ponchick/ZS-Scorpion-256-Turbo-Plus/Scorpion/Scorpion.kicad_sch

## KiCad design Scorpion/Scorpion.kicad_sch (2023-03-14)

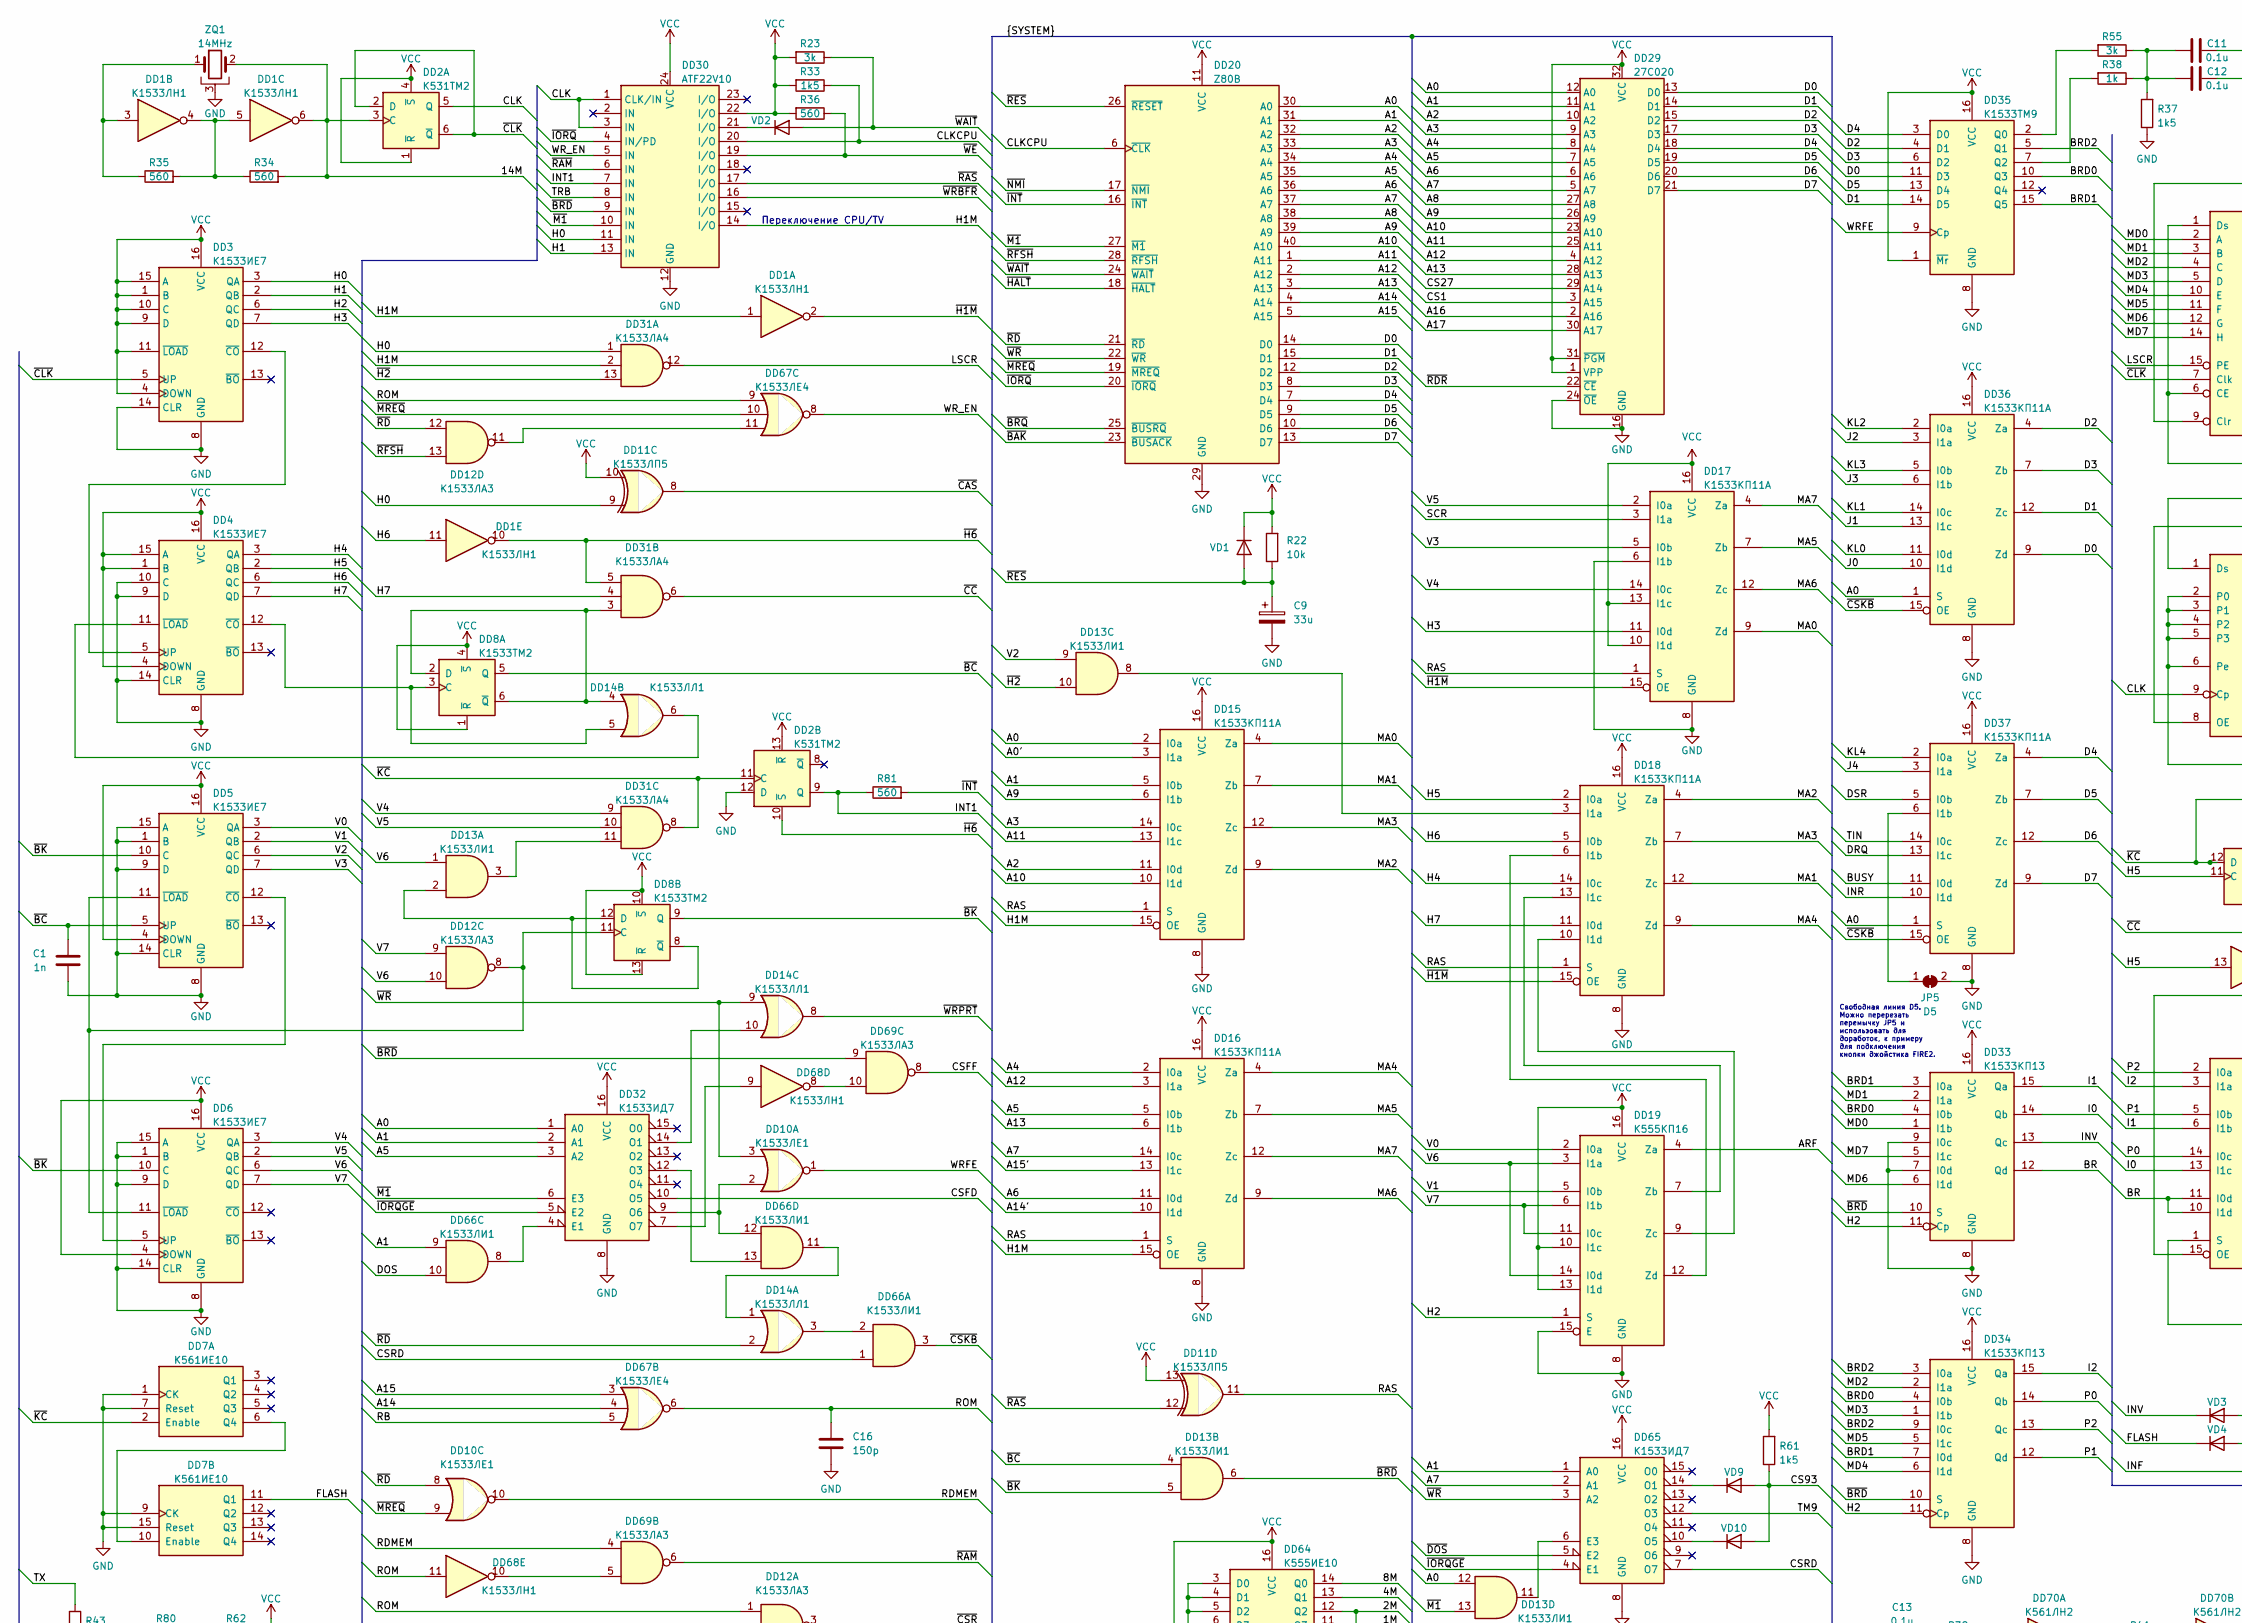
[picture p7: schematic Scorpion.kicad_sch, part in row 1, column 1]

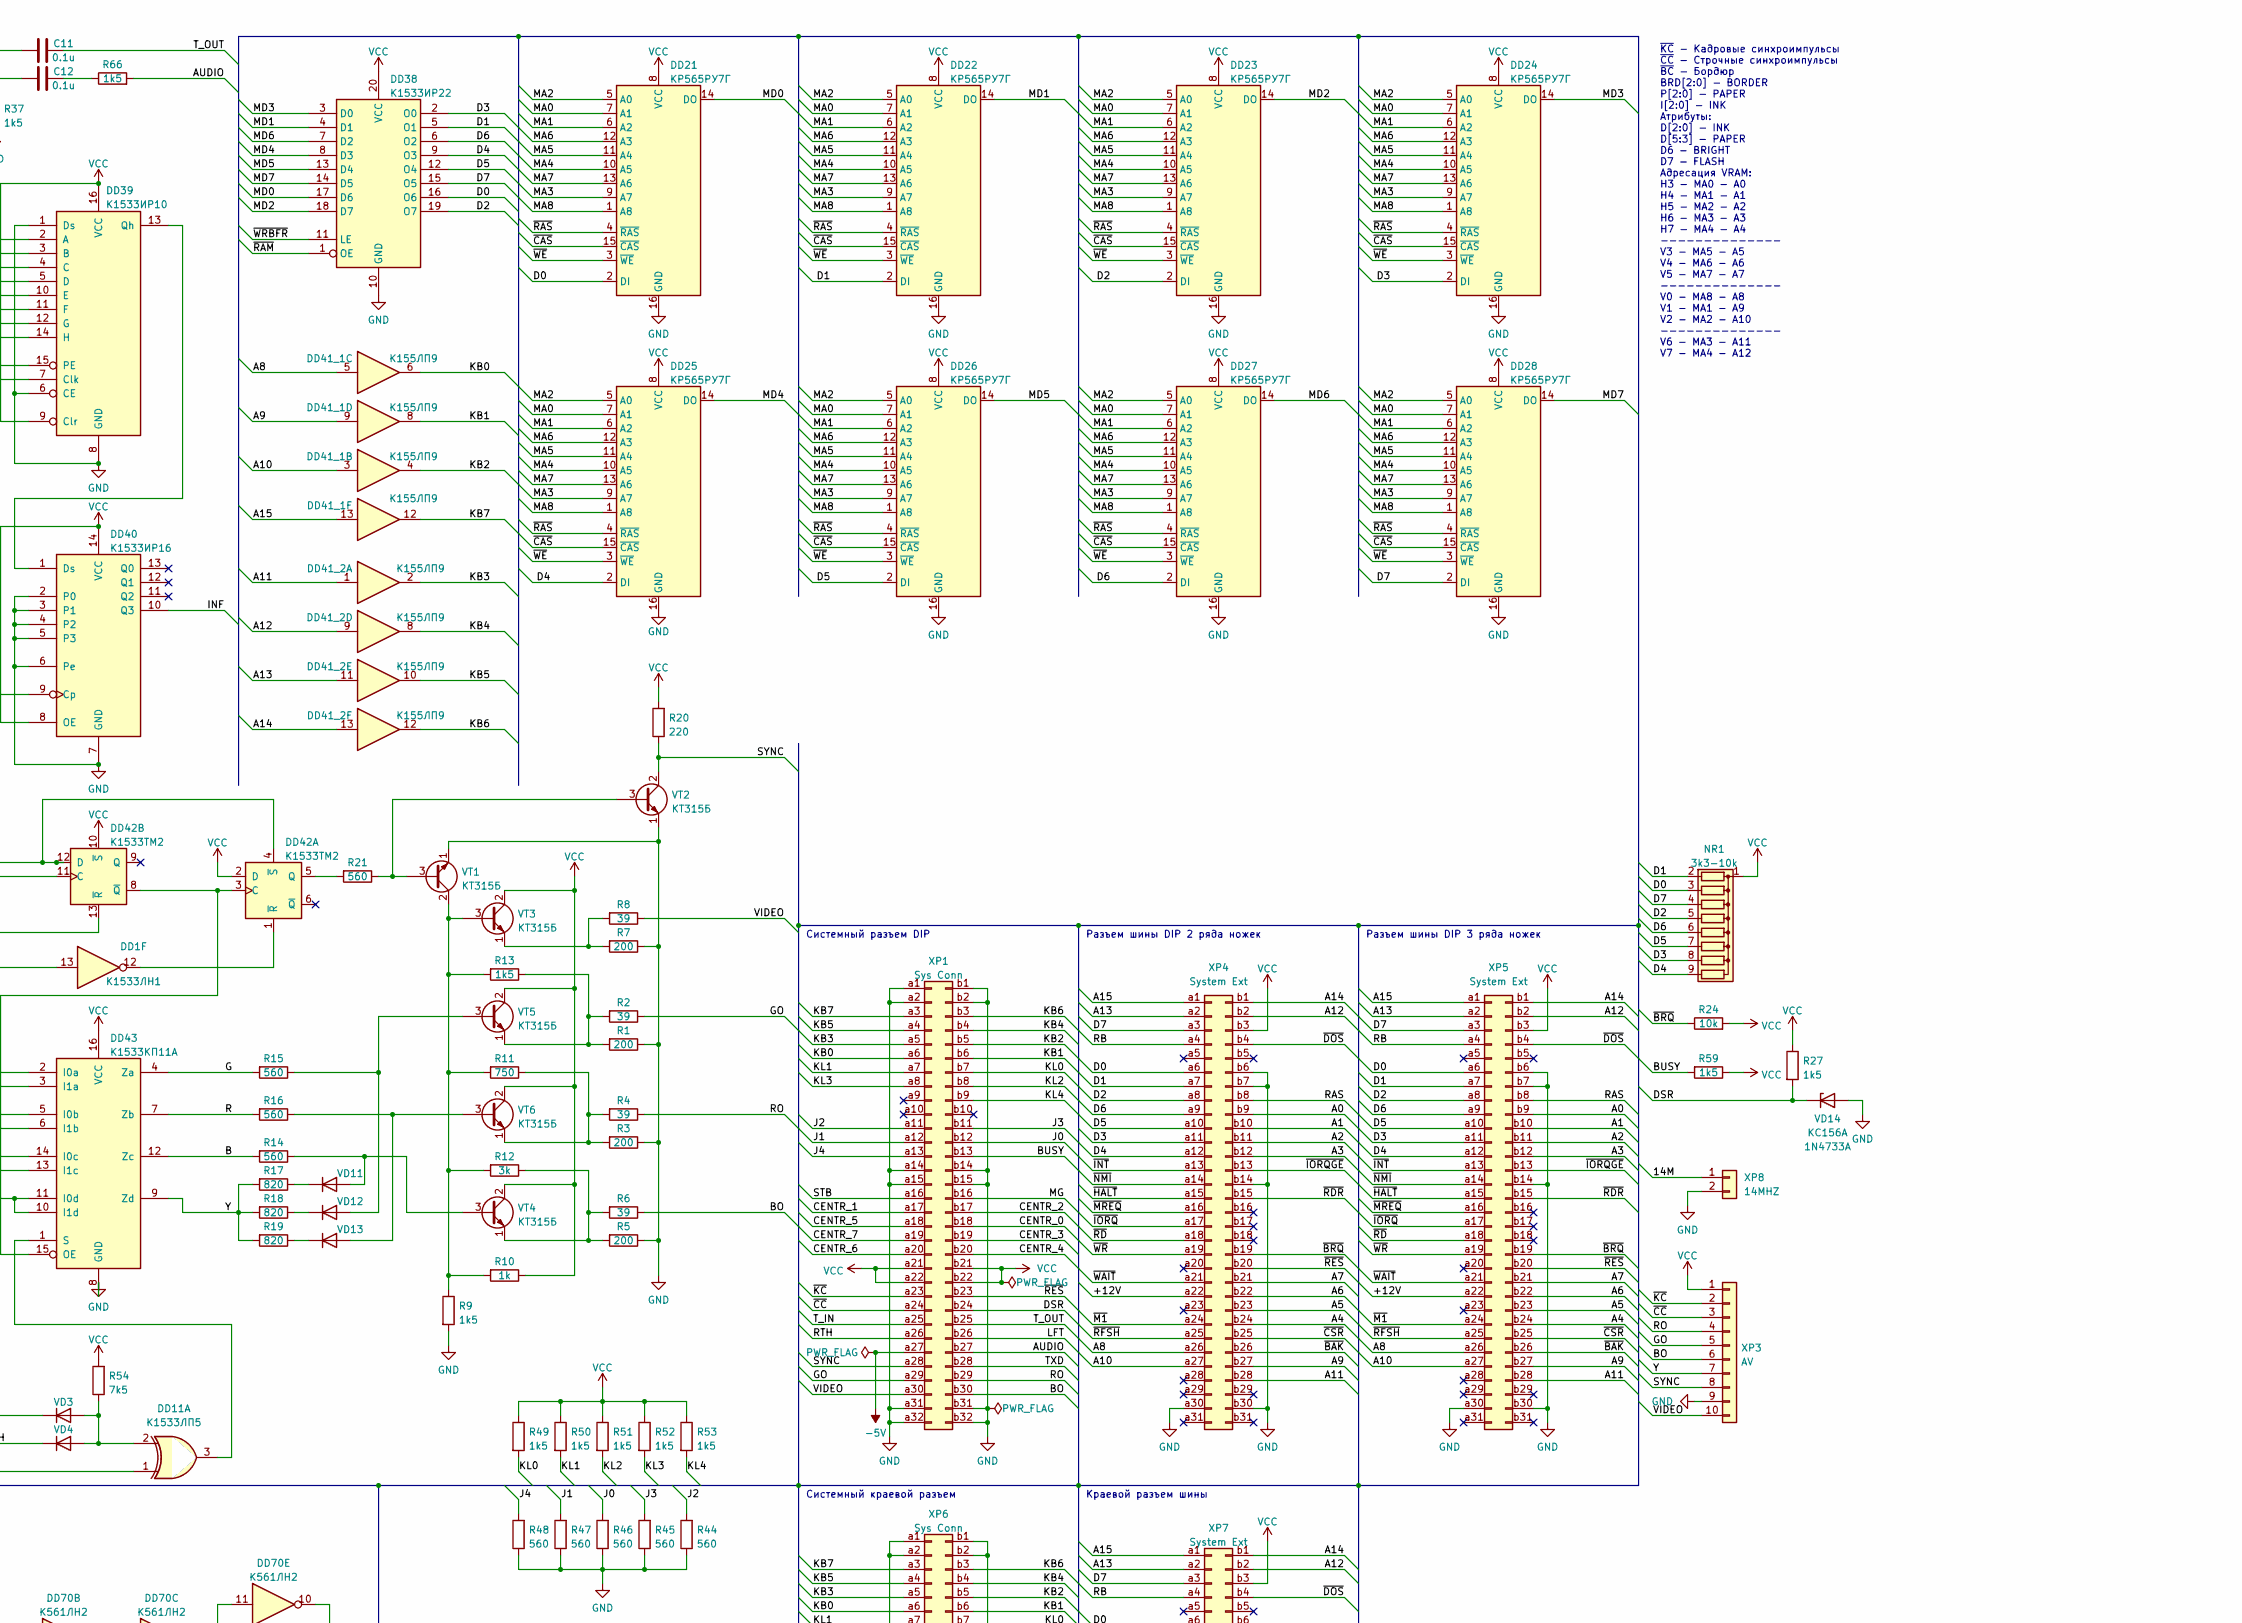
[picture p8: schematic Scorpion.kicad_sch, part in row 1, column 2]

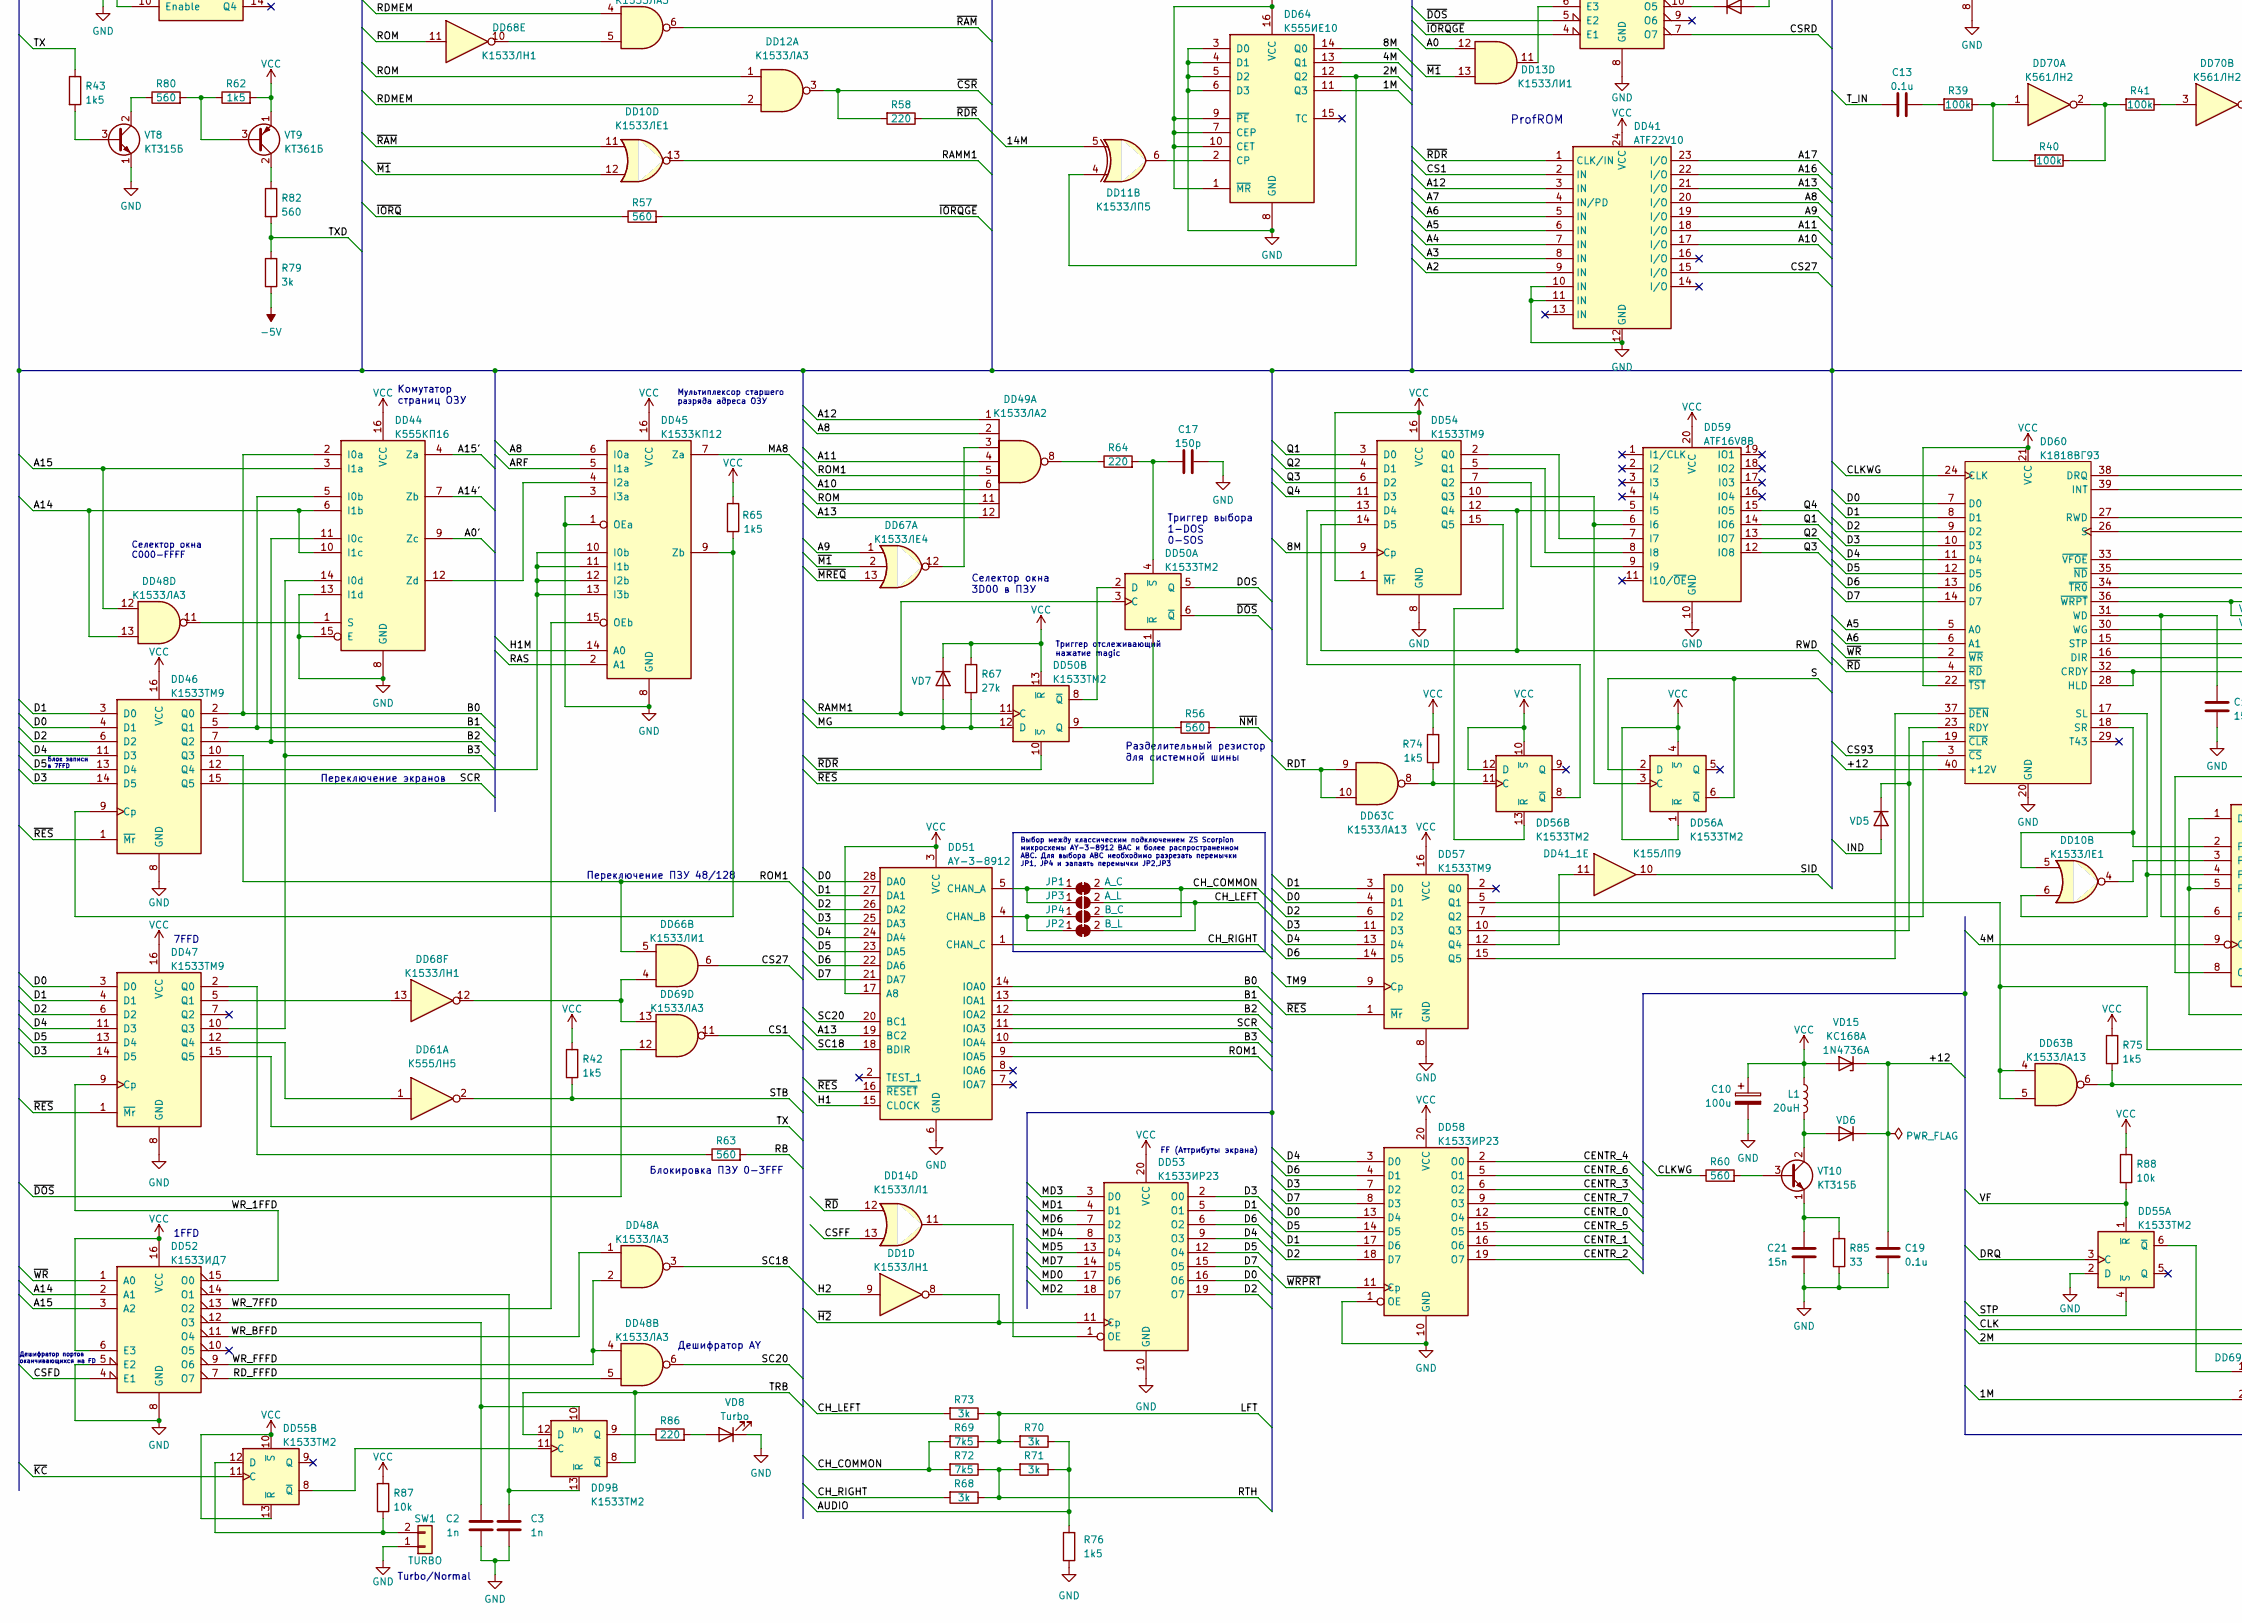
[picture p9: schematic Scorpion.kicad_sch, part in row 2, column 1]

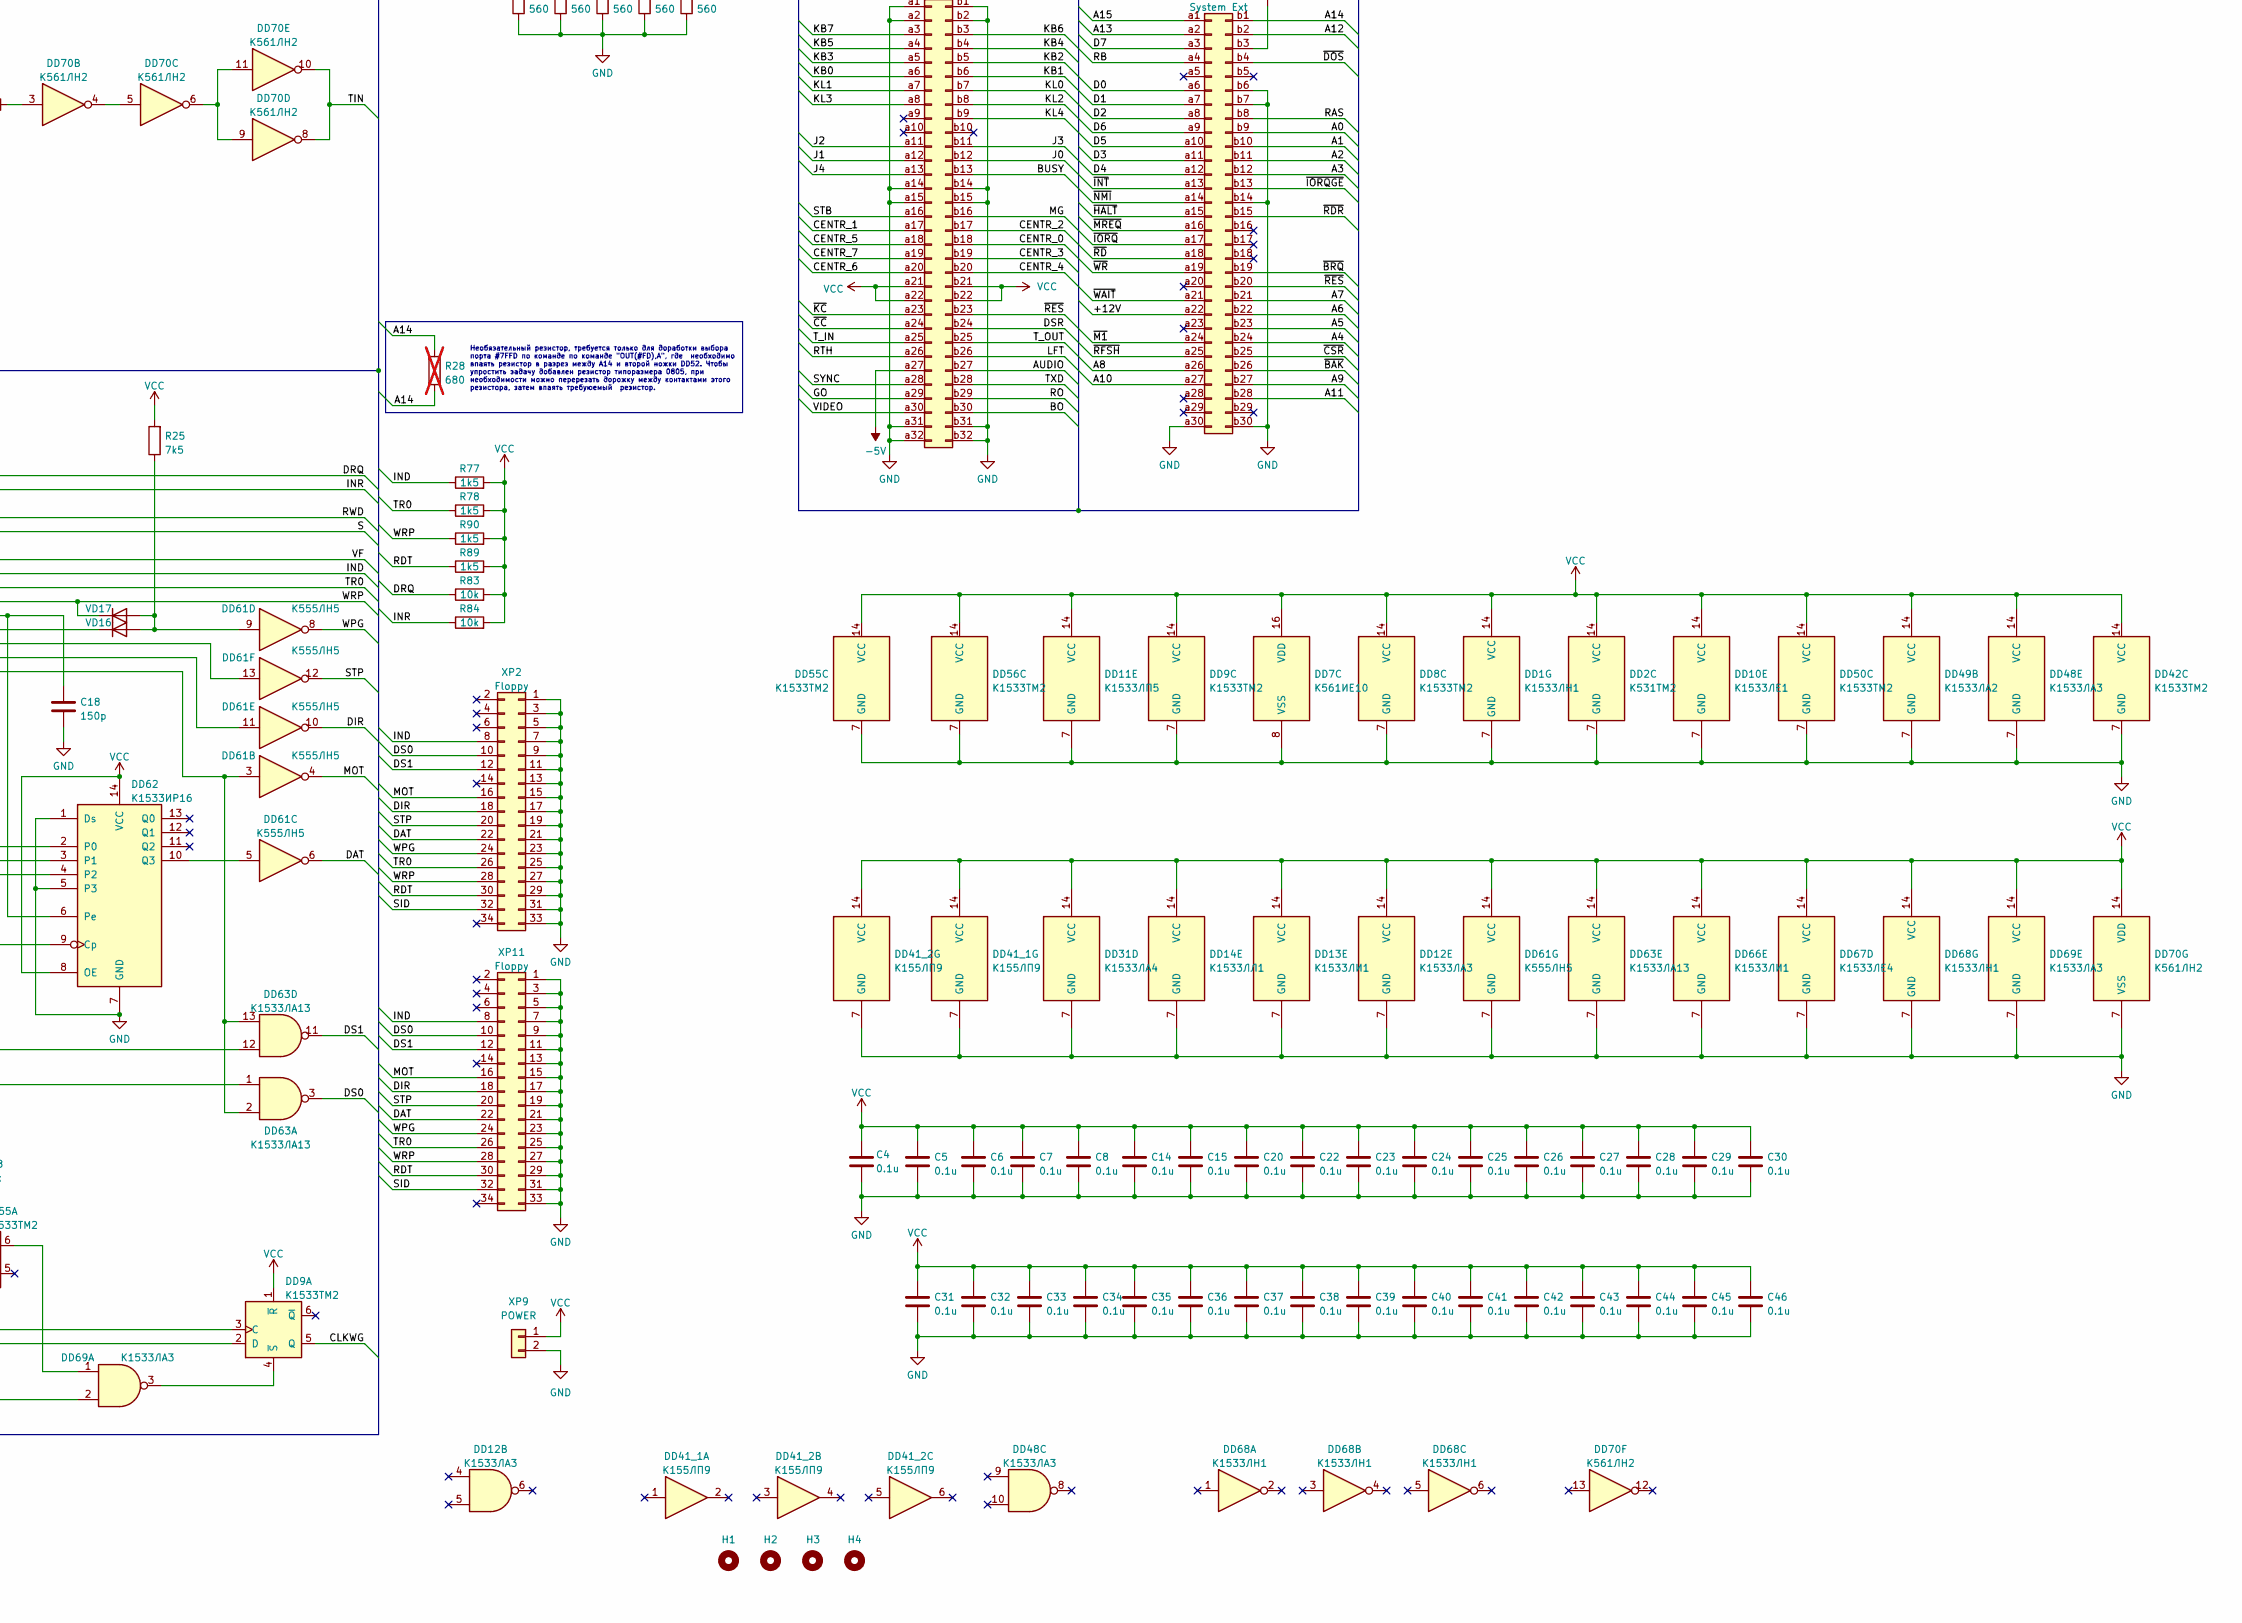
[picture p10: schematic Scorpion.kicad_sch, part in row 2, column 2]

Parts:
C1, C2, C3: 1n; Cap_5.08
C4, C5, C6, C7, C8, C11, C12, C13, C14, C15, C19, C20, C22, C23, C24, C25, C26, C27, C28, C29, C30, C31, C32, C33, C34, C35, C36, C37, C38, C39, C40, C41, C42, C43, C44, C45, C46: 0.1u; Cap_5.08
C9: 33u; CP_Radial_D5.0mm_P2.50mm
C10: 100u; CP_Radial_D6.3mm_P2.50mm
C16, C17, C18: 150p; Cap_5.08
C21: 15n; Cap_5.08
DD1, DD68: К1533ЛН1; DIP-14
DD2: К531ТМ2; DIP-14
DD3, DD4, DD5, DD6: К1533ИЕ7; DIP-16
DD7: К561ИЕ10; DIP-16
DD8, DD9, DD42, DD50, DD55, DD56: К1533ТМ2; DIP-14
DD10: К1533ЛЕ1; DIP-14
DD11: К1533ЛП5; DIP-14
DD12, DD48, DD69: К1533ЛА3; DIP-14
DD13, DD66: К1533ЛИ1; DIP-14
DD14: К1533ЛЛ1; DIP-14
DD15, DD16, DD17, DD18, DD36, DD37, DD43: К1533КП11A; DIP-16
DD19, DD44: К555КП16; DIP-16
DD20: Z80B; DIP-40-S
DD21, DD22, DD23, DD24, DD25, DD26, DD27, DD28: КР565РУ7Г; DIP-16-S
DD29: 27C020; DIP-32-S
DD30: ATF22V10; DIP-24-S
DD31: К1533ЛА4; DIP-14
DD32, DD52, DD65: К1533ИД7; DIP-16
DD33, DD34: К1533КП13; DIP-16
DD35, DD46, DD47, DD54, DD57: К1533ТМ9; DIP-16
DD38: К1533ИР22; DIP-20
DD39: К1533ИР10; DIP-16
DD40, DD62: К1533ИР16; DIP-14
DD41: ATF22V10; DIP-24
DD41_1, DD41_2: К155ЛП9; DIP-14
DD45: К1533КП12; DIP-16
DD49: К1533ЛА2; DIP-14
DD51: AY-3-8912; DIP-28W-S
DD53, DD58: К1533ИР23; DIP-20
DD59: ATF16V8B; DIP-20
DD60: К1818ВГ93; DIP-40-S
DD61: К555ЛН5; DIP-14
DD63: К1533ЛА13; DIP-14
DD64: К555ИЕ10; DIP-16
DD67: К1533ЛЕ4; DIP-14
DD70: К561ЛН2; DIP-14
H1, H2, H3, H4: MountingHole_3.2mm_M3
JP1: A_C; SolderJumper-2_P1.3mm_Bridged_RoundedPad1.0x1.5mm
JP2: B_L; SolderJumper-2_P1.3mm_Bridged_RoundedPad1.0x1.5mm
JP3: A_L; SolderJumper-2_P1.3mm_Open_RoundedPad1.0x1.5mm
JP4: B_C; SolderJumper-2_P1.3mm_Open_RoundedPad1.0x1.5mm
JP5: D5; SolderJumper-2_P1.3mm_Bridged_RoundedPad1.0x1.5mm
L1: 20uH; L_Axial_L5.3mm_D2.2mm_P7.62mm_Horizontal_Vishay_IM-1
NR1: 3k3-10k; RN_9
R1, R3, R5, R7: 200; R_7.62
R2, R4, R6, R8: 39; R_7.62
R9, R13, R27, R33, R37, R42, R43, R49, R50, R51, R52, R53, R59, R61, R62, R65, R66, R74, R75, R76, R77, R78, R89, R90: 1k5; R_7.62
R10, R38: 1k; R_7.62
R11: 750; R_7.62
R12, R23, R55, R68, R70, R71, R73, R79: 3k; R_7.62
R14, R15, R16, R21, R34, R35, R36, R44, R45, R46, R47, R48, R56, R57, R60, R63, R80, R81, R82: 560; R_7.62
R17, R18, R19: 820; R_7.62
R20, R58, R64, R86: 220; R_7.62
R22, R24, R83, R84, R87, R88: 10k; R_7.62
R25, R54, R69, R72: 7k5; R_7.62
R28: 680; R_0805_2012Metric; not fitted
R39, R40, R41: 100k; R_7.62
R67: 27k; R_7.62
R85: 33; R_7.62
SW1: TURBO; PinHeader_1x02_P2.54mm_Vertical
VD1, VD2, VD3, VD4, VD5, VD6, VD7, VD9, VD10, VD11, VD12, VD13, VD16, VD17: КД522А; DO-35
VD8: Turbo; LED_D3.0mm
VD14: КС156А; DO-35
VD15: КС168А; DO-35
VT1, VT2, VT3, VT4, VT5, VT6, VT8, VT10: КТ315Б; КТ-13
VT9: КТ361Б; КТ-13
XP1: Sys Conn; CONN_2x32
XP2: Floppy; CONN_2x17
XP3: AV; CONN_1x10
XP4: System Ext; CONN_2x31_WIDE
XP5: System Ext; CONN_3x31
XP6: Sys Conn; CONN_2x32_EDGE_2.52
XP7: System Ext; CONN_2x30_EDGE_2.52
XP8: 14MHZ; PinHeader_1x02_P2.54mm_Vertical
XP9: POWER; PinHeader_1x02_P2.54mm_Vertical
XP11: Floppy; CONN_2x17_EDGE_NARROW
ZQ1: 14MHz; Crystal_HC49-U_Horizontal_1EP_style2

Connections:
1M: DD64.11 (Q3), DD69.2
2M: DD9.2 (D), DD11.4, DD64.12 (Q2)
4M: DD62.9 (Cp), DD64.13 (Q1)
8M: DD54.9 (Cp), DD64.14 (Q0)
14M: DD1.6, DD2.3 (C), DD11.5, R34.2, XP8.1, ZQ1.2
+12: C19.1, DD60.40 (+12V), VD6.1 (K), VD15.1 (K)
+12V: XP4.a22, XP5.a22, XP7.a22
-5V: R79.1, XP1.a27, XP6.a27
A0: DD13.12, DD15.2 (I0a), DD20.30 (A0), DD29.12 (A0), DD32.1 (A0), DD36.1 (S), DD37.1 (S), XP4.b9, XP5.b9, XP7.b9
A0': DD15.3 (I1a), DD44.9 (Zc)
A1: DD15.5 (I0b), DD20.31 (A1), DD29.11 (A1), DD32.2 (A1), DD65.1 (A0), DD66.9, XP4.b10, XP5.b10, XP7.b10
A2: DD15.11 (I0d), DD20.32 (A2), DD29.10 (A2), DD41.9 (IN), XP4.b11, XP5.b11, XP7.b11
A3: DD15.14 (I0c), DD20.33 (A3), DD29.9 (A3), DD41.8 (IN), XP4.b12, XP5.b12, XP7.b12
A4: DD16.2 (I0a), DD20.34 (A4), DD29.8 (A4), DD41.7 (IN), XP4.b24, XP5.b24, XP7.b24
A5: DD16.5 (I0b), DD20.35 (A5), DD29.7 (A5), DD32.3 (A2), DD41.6 (IN), DD60.5 (A0), XP4.b23, XP5.b23, XP7.b23
A6: DD16.11 (I0d), DD20.36 (A6), DD29.6 (A6), DD41.5 (IN), DD60.6 (A1), XP4.b22, XP5.b22, XP7.b22
A7: DD16.14 (I0c), DD20.37 (A7), DD29.5 (A7), DD41.4 (IN/PD), DD65.2 (A1), XP4.b21, XP5.b21, XP7.b21
A8: DD20.38 (A8), DD29.27 (A8), DD41.20 (I/O), DD41_1.5, DD45.6 (I0a), DD49.2, XP4.a26, XP5.a26, XP7.a26
A9: DD15.6 (I1b), DD20.39 (A9), DD29.26 (A9), DD41.19 (I/O), DD41_1.9, DD67.1, XP4.b27, XP5.b27, XP7.b27
A10: DD15.10 (I1d), DD20.40 (A10), DD29.23 (A10), DD41.17 (I/O), DD41_1.3, DD49.6, XP4.a27, XP5.a27, XP7.a27
A11: DD15.13 (I1c), DD20.1 (A11), DD29.25 (A11), DD41.18 (I/O), DD41_2.1, DD49.4, XP4.b28, XP5.b28, XP7.b28
A12: DD16.3 (I1a), DD20.2 (A12), DD29.4 (A12), DD41.3 (IN), DD41_2.9, DD49.1, XP4.b2, XP5.b2, XP7.b2
A13: DD16.6 (I1b), DD20.3 (A13), DD29.28 (A13), DD41.21 (I/O), DD41_2.11, DD49.12, DD51.19 (BC2), XP4.a2, XP5.a2, XP7.a2
A14: DD20.4 (A14), DD41_2.13, DD44.6 (I1b), DD44.10 (I1c), DD48.13, DD52.2 (A1), DD67.4, R28.1, R28.2, XP4.b1, XP5.b1, XP7.b1
A14': DD16.10 (I1d), DD44.7 (Zb)
A15: DD20.5 (A15), DD41_1.13, DD44.3 (I1a), DD48.12, DD52.3 (A2), DD67.3, XP4.a1, XP5.a1, XP7.a1
A15': DD16.13 (I1c), DD44.4 (Za)
A16: DD29.2 (A16), DD41.22 (I/O)
A17: DD29.30 (A17), DD41.23 (I/O)
ARF: DD19.4 (Za), DD45.5 (I1a)
AUDIO: R66.2, R70.1, R71.1, R76.2, XP1.b27, XP6.b27
B: DD43.12 (Zc), R14.2
B0: DD44.2 (I0a), DD46.2 (Q0), DD51.14 (IOA0)
B1: DD44.5 (I0b), DD46.5 (Q1), DD51.13 (IOA1)
B2: DD44.11 (I0c), DD46.7 (Q2), DD51.12 (IOA2)
B3: DD44.14 (I0d), DD47.10 (Q3), DD51.10 (IOA4)
BO: R6.1, XP1.b30, XP3.6, XP6.b30
BR: DD33.12 (Qd), DD43.10 (I1d), DD43.11 (I0d)
BRD0: DD33.4 (I0b), DD34.4 (I0b), DD35.10 (Q3)
BRD1: DD33.3 (I0a), DD34.7 (I0d), DD35.15 (Q5)
BRD2: DD34.3 (I0a), DD34.9 (I0c), DD35.5 (Q1)
BUSY: DD37.11 (I0d), R59.2, XP1.b13, XP6.b13
CENTR_0: DD58.12 (O4), XP1.b18, XP6.b18
CENTR_1: DD58.16 (O6), XP1.a17, XP6.a17
CENTR_2: DD58.19 (O7), XP1.b17, XP6.b17
CENTR_3: DD58.6 (O2), XP1.b19, XP6.b19
CENTR_4: DD58.2 (O0), XP1.b20, XP6.b20
CENTR_5: DD58.15 (O5), XP1.a18, XP6.a18
CENTR_6: DD58.5 (O1), XP1.a20, XP6.a20
CENTR_7: DD58.9 (O3), XP1.a19, XP6.a19
CH_COMMON: JP1.2 (B), JP4.2 (B), R69.2, R72.2
CH_LEFT: JP2.2 (B), JP3.2 (B), R73.2
CH_RIGHT: DD51.1 (CHAN_C), R68.2
CLK: DD2.5 (Q), DD9.3 (C), DD30.1 (CLK/IN), DD30.3 (IN), DD40.9 (Cp)
CLKCPU: DD20.6 (~CLK), DD30.20 (I/O), R33.1
CLKWG: DD9.5 (Q), DD60.24 (CLK), R60.1
CS1: DD29.3 (A15), DD41.2 (IN), DD69.11
CS27: DD29.29 (A14), DD41.15 (I/O), DD66.6
CS93: DD60.3 (~CS), R61.1, VD9.2 (A), VD10.2 (A)
CSFD: DD32.10 (O5), DD52.4 (E1)
CSFF: DD14.13, DD69.8
CSRD: DD65.7 (O7), DD66.1
D0: DD20.14 (D0), DD21.2 (DI), DD29.13 (D0), DD35.11 (D3), DD36.9 (Zd), DD38.16 (O6), DD46.4 (D1), DD47.3 (D0), DD51.28 (DA0), DD53.16 (O6), DD57.4 (D1), DD58.13 (D4), DD60.7 (D0), NR1.3 (R2), XP4.a6, XP5.a6, XP7.a6
D1: DD20.15 (D1), DD22.2 (DI), DD29.14 (D1), DD35.14 (D5), DD36.12 (Zc), DD38.5 (O1), DD46.3 (D0), DD47.4 (D1), DD51.27 (DA1), DD53.5 (O1), DD57.3 (D0), DD58.17 (D6), DD60.8 (D1), NR1.2 (R1), XP4.a7, XP5.a7, XP7.a7
D2: DD20.12 (D2), DD23.2 (DI), DD29.15 (D2), DD35.4 (D1), DD36.4 (Za), DD38.19 (O7), DD46.6 (D2), DD47.6 (D2), DD51.26 (DA2), DD53.19 (O7), DD57.6 (D2), DD58.18 (D7), DD60.9 (D2), NR1.5 (R4), XP4.a8, XP5.a8, XP7.a8
D3: DD20.8 (D3), DD24.2 (DI), DD29.17 (D3), DD35.6 (D2), DD36.7 (Zb), DD38.2 (O0), DD46.14 (D5), DD47.14 (D5), DD51.25 (DA3), DD53.2 (O0), DD57.11 (D3), DD58.7 (D2), DD60.10 (D3), NR1.8 (R7), XP4.a11, XP5.a11, XP7.a11
D4: DD20.7 (D4), DD25.2 (DI), DD29.18 (D4), DD35.3 (D0), DD37.4 (Za), DD38.9 (O3), DD46.11 (D3), DD47.11 (D3), DD51.24 (DA4), DD53.9 (O3), DD57.13 (D4), DD58.3 (D0), DD60.11 (D4), NR1.9 (R8), XP4.a12, XP5.a12, XP7.a12
D5: DD20.9 (D5), DD26.2 (DI), DD29.19 (D5), DD35.13 (D4), DD37.7 (Zb), DD38.12 (O4), DD46.13 (D4), DD47.13 (D4), DD51.23 (DA5), DD53.12 (O4), DD58.14 (D5), DD60.12 (D5), NR1.7 (R6), XP4.a10, XP5.a10, XP7.a10
D6: DD20.10 (D6), DD27.2 (DI), DD29.20 (D6), DD37.12 (Zc), DD38.6 (O2), DD51.22 (DA6), DD53.6 (O2), DD57.14 (D5), DD58.4 (D1), DD60.13 (D6), NR1.6 (R5), XP4.a9, XP5.a9, XP7.a9
D7: DD20.13 (D7), DD28.2 (DI), DD29.21 (D7), DD37.9 (Zd), DD38.15 (O5), DD51.21 (DA7), DD53.15 (O5), DD58.8 (D3), DD60.14 (D7), NR1.4 (R3), XP4.a3, XP5.a3, XP7.a3
DAT: DD61.6, XP2.22, XP11.22
DIR: DD61.10, XP2.18, XP11.18
DOS: DD50.5 (Q), DD66.10
DRQ: DD37.13 (I1c), DD55.3 (C), DD60.38 (DRQ), R83.1
DS0: DD63.3, XP2.10, XP11.10
DS1: DD63.11, XP2.12, XP11.12
DSR: DD37.5 (I0b), R27.2, VD14.1 (K), XP1.b24, XP6.b24
FLASH: DD7.11 (Q1), VD4.1 (K)
G: DD43.4 (Za), R15.2
GND: C1.2, C2.2, C3.2, C4.1, C5.1, C6.1, C7.1, C8.1, C9.2, C10.2, C14.1, C15.1, C16.1, C17.1, C18.2, C19.2, C20.1, C21.2, C22.1, C23.1, C24.1, C25.1, C26.1, C27.1, C28.1, C29.1, C30.1, C31.1, C32.1, C33.1, C34.1, C35.1, C36.1, C37.1, C38.1, C39.1, C40.1, C41.1, C42.1, C43.1, C44.1, C45.1, C46.1, DD1.7 (GND), DD2.7 (GND), DD2.12 (D), DD3.8 (GND), DD3.14 (CLR), DD4.8 (GND), DD4.9 (D), DD4.10 (C), DD4.14 (CLR), DD5.1 (B), DD5.8 (GND), DD5.9 (D), DD5.14 (CLR), DD5.15 (A), DD6.1 (B), DD6.8 (GND), DD6.9 (D), DD6.14 (CLR), DD6.15 (A), DD7.1 (CK), DD7.7 (Reset), DD7.8 (VSS), DD7.9 (CK), DD7.15 (Reset), DD8.7 (GND), DD9.7 (GND), DD10.7 (GND), DD11.7 (GND), DD12.7 (GND), DD13.7 (GND), DD14.7 (GND), DD15.8 (GND), DD16.8 (GND), DD17.6 (I1b), DD17.8 (GND), DD18.8 (GND), DD19.8 (GND), DD19.15 (E), DD20.29 (GND), DD21.16 (GND), DD22.16 (GND), DD23.16 (GND), DD24.16 (GND), DD25.16 (GND), DD26.16 (GND), DD27.16 (GND), DD28.16 (GND), DD29.16 (GND), DD29.24 (~OE), DD30.12 (GND), DD31.7 (GND), DD32.8 (GND), DD33.7 (I0d), DD33.8 (GND), DD33.9 (I0c), DD34.8 (GND), DD35.8 (GND), DD36.8 (GND), DD37.8 (GND), DD38.10 (GND), DD39.1 (Ds), DD39.6 (CE), DD39.8 (GND), DD40.2 (P0), DD40.3 (P1), DD40.4 (P2), DD40.5 (P3), DD40.6 (Pe), DD40.7 (GND), DD41.10 (IN), DD41.11 (IN), DD41.12 (GND), DD41_1.7 (GND), DD41_2.7 (GND), DD42.7 (GND), DD43.8 (GND), DD44.8 (GND), DD44.13 (I1d), DD44.15 (E), DD45.1 (OEa), DD45.3 (I3a), DD45.8 (GND), DD46.8 (GND), DD47.8 (GND), DD48.7 (GND), DD49.7 (GND), DD50.7 (GND), DD51.6 (GND), DD52.5 (E2), DD52.8 (GND), DD53.10 (GND), DD54.8 (GND), DD55.2 (D), DD55.7 (GND), DD56.7 (GND), DD57.8 (GND), DD58.1 (OE), DD58.10 (GND), DD59.10 (GND), DD60.20 (GND), DD61.7 (GND), DD62.1 (Ds), DD62.5 (P3), DD62.7 (GND), DD63.7 (GND), DD64.3 (D0), DD64.4 (D1), DD64.5 (D2), DD64.6 (D3), DD64.8 (GND), DD65.8 (GND), DD66.7 (GND), DD67.7 (GND), DD68.7 (GND), DD69.7 (GND), DD70.7 (VSS), JP5.2 (B), R1.1, R3.1, R5.1, R7.1, R9.2, R37.1, R44.1, R45.1, R46.1, R47.1, R48.1, R76.1, R85.1, SW1.1, VD8.1 (K), VD14.2 (A), VT1.1 (E), VT2.1 (E), VT8.1 (E), XP1.a1, XP1.a2, XP1.a14, XP1.a15, XP1.a31, XP1.a32, XP1.b1, XP1.b2, XP1.b14, XP1.b15, XP1.b31, XP1.b32, XP2.1, XP2.3, XP2.5, XP2.7, XP2.9, XP2.11, XP2.13, XP2.15, XP2.17, XP2.19, XP2.21, XP2.23, XP2.25, XP2.27, XP2.29, XP2.31, XP2.33, XP3.9, XP4.a30, XP4.b6, XP4.b7, XP4.b14, XP4.b30, XP5.a30, XP5.b6, XP5.b7, XP5.b14, XP5.b30, XP6.a1, XP6.a2, XP6.a14, XP6.a15, XP6.a31, XP6.a32, XP6.b1, XP6.b2, XP6.b14, XP6.b15, XP6.b31, XP6.b32, XP7.a30, XP7.b6, XP7.b7, XP7.b14, XP7.b30, XP8.2, XP9.2, XP11.1, XP11.3, XP11.5, XP11.7, XP11.9, XP11.11, XP11.13, XP11.15, XP11.17, XP11.19, XP11.21, XP11.23, XP11.25, XP11.27, XP11.29, XP11.31, XP11.33, ZQ1.3
GO: R2.1, XP1.a29, XP3.5, XP6.a29
H0: DD3.3 (QA), DD11.9, DD30.11 (IN), DD31.1
H1: DD3.2 (QB), DD30.13 (IN), DD51.15 (CLOCK)
H1M: DD1.1, DD15.15 (OE), DD16.15 (OE), DD30.14 (I/O), DD31.2, DD45.14 (A0)
H2: DD1.9, DD3.6 (QC), DD19.1 (S), DD33.11 (Cp), DD34.11 (Cp)
H3: DD3.7 (QD), DD17.11 (I0d)
H4: DD4.3 (QA), DD18.14 (I0c)
H5: DD1.13, DD4.2 (QB), DD18.2 (I0a), DD42.11 (C)
H6: DD1.11, DD4.6 (QC), DD18.5 (I0b)
H7: DD4.7 (QD), DD18.11 (I0d), DD31.4
I0: DD33.14 (Qb), DD43.13 (I1c)
I1: DD33.15 (Qa), DD43.6 (I1b)
I2: DD34.15 (Qa), DD43.3 (I1a)
IND: DD60.35 (~ND), R77.1, VD5.2 (A), XP2.8, XP11.8
INF: DD11.1, DD40.10 (Q3)
INR: DD37.10 (I1d), DD60.39 (INT), R84.1
INT1: DD2.9 (Q), DD30.7 (IN), R81.1
INV: DD33.13 (Qc), VD3.1 (K)
J0: DD36.10 (I1d), R46.2, XP1.b12, XP6.b12
J1: DD36.13 (I1c), R47.2, XP1.a12, XP6.a12
J2: DD36.3 (I1a), R44.2, XP1.a11, XP6.a11
J3: DD36.6 (I1b), R45.2, XP1.b11, XP6.b11
J4: DD37.3 (I1a), R48.2, XP1.a13, XP6.a13
KB0: DD41_1.6, XP1.a6, XP6.a6
KB1: DD41_1.8, XP1.b6, XP6.b6
KB2: DD41_1.4, XP1.b5, XP6.b5
KB3: DD41_2.2, XP1.a5, XP6.a5
KB4: DD41_2.8, XP1.b4, XP6.b4
KB5: DD41_2.10, XP1.a4, XP6.a4
KB6: DD41_2.12, XP1.b3, XP6.b3
KB7: DD41_1.12, XP1.a3, XP6.a3
KL0: DD36.11 (I0d), R49.2, XP1.b7, XP6.b7
KL1: DD36.14 (I0c), R50.2, XP1.a7, XP6.a7
KL2: DD36.2 (I0a), R51.2, XP1.b8, XP6.b8
KL3: DD36.5 (I0b), R52.2, XP1.a8, XP6.a8
KL4: DD37.2 (I0a), R53.2, XP1.b9, XP6.b9
LFT: R69.1, R70.2, R73.1, XP1.b26, XP6.b26
LSCR: DD31.12, DD39.15 (PE)
MA0: DD15.4 (Za), DD17.9 (Zd), DD21.7 (A1), DD22.7 (A1), DD23.7 (A1), DD24.7 (A1), DD25.7 (A1), DD26.7 (A1), DD27.7 (A1), DD28.7 (A1)
MA1: DD15.7 (Zb), DD18.12 (Zc), DD21.6 (A2), DD22.6 (A2), DD23.6 (A2), DD24.6 (A2), DD25.6 (A2), DD26.6 (A2), DD27.6 (A2), DD28.6 (A2)
MA2: DD15.9 (Zd), DD18.4 (Za), DD21.5 (A0), DD22.5 (A0), DD23.5 (A0), DD24.5 (A0), DD25.5 (A0), DD26.5 (A0), DD27.5 (A0), DD28.5 (A0)
MA3: DD15.12 (Zc), DD18.7 (Zb), DD21.9 (A7), DD22.9 (A7), DD23.9 (A7), DD24.9 (A7), DD25.9 (A7), DD26.9 (A7), DD27.9 (A7), DD28.9 (A7)
MA4: DD16.4 (Za), DD18.9 (Zd), DD21.10 (A5), DD22.10 (A5), DD23.10 (A5), DD24.10 (A5), DD25.10 (A5), DD26.10 (A5), DD27.10 (A5), DD28.10 (A5)
MA5: DD16.7 (Zb), DD17.7 (Zb), DD21.11 (A4), DD22.11 (A4), DD23.11 (A4), DD24.11 (A4), DD25.11 (A4), DD26.11 (A4), DD27.11 (A4), DD28.11 (A4)
MA6: DD16.9 (Zd), DD17.12 (Zc), DD21.12 (A3), DD22.12 (A3), DD23.12 (A3), DD24.12 (A3), DD25.12 (A3), DD26.12 (A3), DD27.12 (A3), DD28.12 (A3)
MA7: DD16.12 (Zc), DD17.4 (Za), DD21.13 (A6), DD22.13 (A6), DD23.13 (A6), DD24.13 (A6), DD25.13 (A6), DD26.13 (A6), DD27.13 (A6), DD28.13 (A6)
MA8: DD21.1 (A8), DD22.1 (A8), DD23.1 (A8), DD24.1 (A8), DD25.1 (A8), DD26.1 (A8), DD27.1 (A8), DD28.1 (A8), DD45.7 (Za)
MD0: DD21.14 (DO), DD33.1 (I1b), DD38.17 (D6), DD39.2 (A), DD53.17 (D6)
MD1: DD22.14 (DO), DD33.2 (I1a), DD38.4 (D1), DD39.3 (B), DD53.4 (D1)
MD2: DD23.14 (DO), DD34.2 (I1a), DD38.18 (D7), DD39.4 (C), DD53.18 (D7)
MD3: DD24.14 (DO), DD34.1 (I1b), DD38.3 (D0), DD39.5 (D), DD53.3 (D0)
MD4: DD25.14 (DO), DD34.6 (I1d), DD38.8 (D3), DD39.10 (E), DD53.8 (D3)
MD5: DD26.14 (DO), DD34.5 (I1c), DD38.13 (D4), DD39.11 (F), DD53.13 (D4)
MD6: DD27.14 (DO), DD33.6 (I1d), DD38.7 (D2), DD39.12 (G), DD53.7 (D2)
MD7: DD28.14 (DO), DD33.5 (I1c), DD38.14 (D5), DD39.14 (H), DD53.14 (D5)
MG: DD50.12 (D), R67.2, VD7.2 (A), XP1.b16, XP6.b16
MOT: DD61.4, XP2.16, XP11.16
unnamed: C2.1, DD9.10 (~S), DD52.12 (O3)
unnamed: C3.1, DD9.13 (~R), DD52.14 (O1)
unnamed: C11.2, C12.2, R37.2, R38.1, R55.1
unnamed: C12.1, R66.1
unnamed: C13.1, R39.2
unnamed: C17.2, DD50.4 (~S), R64.2
unnamed: C18.1, DD60.31 (WD), DD62.6 (Pe)
unnamed: C21.1, R85.2, VT10.1 (E)
unnamed: DD1.3, R35.1, ZQ1.1
unnamed: DD1.4, DD1.5, R34.1, R35.2
unnamed: DD1.12, DD42.1 (~R)
unnamed: DD3.12 (~CO), DD4.5 (UP)
unnamed: DD5.12 (~CO), DD6.5 (UP)
unnamed: DD7.6 (Q4), DD7.10 (Enable)
unnamed: DD9.9 (Q), R86.1
unnamed: DD10.2, DD32.9 (O6), DD66.12
unnamed: DD10.4, DD62.3 (P1)
unnamed: DD10.5, DD60.18 (SR), DD62.2 (P0)
unnamed: DD10.6, DD60.17 (SL), DD62.4 (P2)
unnamed: DD11.2, R54.1, VD3.2 (A), VD4.2 (A)
unnamed: DD11.3, DD43.1 (S)
unnamed: DD11.6, DD64.2 (CP)
unnamed: DD5.11 (~LOAD), DD6.11 (~LOAD), DD8.11 (C), DD12.8
unnamed: DD12.11, DD67.11
unnamed: DD8.8 (~Q), DD8.12 (D), DD13.2
unnamed: DD13.3, DD31.11
unnamed: DD13.8, DD18.3 (I1a)
unnamed: DD13.11, DD65.6 (E3)
unnamed: DD14.1, DD66.11
unnamed: DD14.3, DD66.2
unnamed: DD8.2 (D), DD8.6 (~Q), DD14.4, DD31.3
unnamed: DD4.12 (~CO), DD8.3 (C), DD14.5
unnamed: DD4.11 (~LOAD), DD14.6
unnamed: DD14.10, DD32.14 (O1)
unnamed: DD14.11, DD53.1 (OE)
unnamed: DD18.6 (I1b), DD19.12 (Zd)
unnamed: DD18.10 (I1d), DD19.9 (Zc)
unnamed: DD18.13 (I1c), DD19.7 (Zb)
unnamed: DD30.21 (I/O), VD2.1 (K)
unnamed: DD32.4 (E1), DD66.8
unnamed: DD32.7 (O7), DD68.9
unnamed: DD32.12 (O3), DD66.13
unnamed: DD35.2 (Q0), R55.2
unnamed: DD35.7 (Q2), R38.2
unnamed: DD37.6 (I1b), JP5.1 (A)
unnamed: DD39.13 (Qh), DD40.1 (Ds)
unnamed: DD41_1.11, DD57.12 (Q4)
unnamed: DD42.3 (C), DD42.8 (~Q), DD43.15 (OE)
unnamed: DD42.5 (Q), R21.2
unnamed: DD44.1 (S), DD48.11
unnamed: DD44.12 (Zd), DD45.4 (I2a)
unnamed: DD45.9 (Zb), DD46.9 (Cp), R65.2
unnamed: DD45.10 (I0b), DD45.11 (I1b), DD45.12 (I2b), DD45.13 (I3b), DD46.12 (Q4)
unnamed: DD47.2 (Q0), R63.1
unnamed: DD47.5 (Q1), DD68.13
unnamed: DD47.12 (Q4), DD61.1
unnamed: DD49.3, DD67.12
unnamed: DD49.8, R64.1
unnamed: DD50.2 (D), DD50.8 (~Q)
unnamed: DD50.9 (Q), R56.2
unnamed: DD51.4 (CHAN_B), JP2.1 (A), JP4.1 (A)
unnamed: DD51.5 (CHAN_A), JP1.1 (A), JP3.1 (A)
unnamed: DD54.2 (Q0), DD59.7 (I7)
unnamed: DD54.5 (Q1), DD59.8 (I8)
unnamed: DD54.7 (Q2), DD59.9 (I9)
unnamed: DD54.10 (Q3), DD56.3 (C), DD59.6 (I6)
unnamed: DD54.13 (D4), DD56.8 (~Q)
unnamed: DD54.15 (Q5), DD56.13 (~R)
unnamed: DD55.6 (~Q), DD69.1
unnamed: DD9.11 (C), DD55.8 (~Q)
unnamed: DD55.12 (D), R87.1, SW1.2
unnamed: DD56.11 (C), DD63.8, R74.1
unnamed: DD57.5 (Q1), DD63.4, DD63.5, DD63.12
unnamed: DD57.7 (Q2), DD60.19 (~CLR)
unnamed: DD57.10 (Q3), DD60.23 (RDY), VD5.1 (K)
unnamed: DD57.15 (Q5), DD60.37 (~DEN)
unnamed: DD60.15 (STP), DD61.13
unnamed: DD60.16 (DIR), DD61.11
unnamed: DD60.28 (HLD), DD60.32 (CRDY), DD61.3, DD63.2, DD63.13
unnamed: DD60.30 (WG), VD16.1 (K)
unnamed: DD61.5, DD62.10 (Q3)
unnamed: DD61.9, R25.1, VD16.2 (A), VD17.2 (A)
unnamed: DD63.1, DD63.6, R75.1
unnamed: DD65.10 (O5), VD10.1 (K)
unnamed: DD65.14 (O1), VD9.1 (K)
unnamed: DD66.4, DD68.12, DD69.13
unnamed: DD68.8, DD69.10
unnamed: DD68.10, DD69.5
unnamed: DD9.4 (~S), DD69.3
unnamed: DD70.1, R39.1, R40.2
unnamed: DD70.2, R40.1, R41.2
unnamed: DD70.3, R41.1
unnamed: DD70.4, DD70.5
unnamed: DD70.6, DD70.9, DD70.11
unnamed: L1.1, VD6.2 (A), VT10.2 (C)
unnamed: R1.2, R2.2, R13.1, VT5.1 (E)
unnamed: R7.2, R8.2, VT3.1 (E)
unnamed: R9.1, R10.2, R11.2, R12.2, R13.2, VT1.2 (C), VT3.3 (B)
unnamed: R3.2, R4.2, R11.1, VT6.1 (E)
unnamed: R5.2, R6.2, R12.1, VT4.1 (E)
unnamed: R14.1, VD11.2 (A), VT4.3 (B)
unnamed: R15.1, VD12.2 (A), VT5.3 (B)
unnamed: R16.1, VD13.2 (A), VT6.3 (B)
unnamed: R17.1, VD11.1 (K)
unnamed: R18.1, VD12.1 (K)
unnamed: R19.1, VD13.1 (K)
unnamed: R21.1, VT1.3 (B), VT2.3 (B)
unnamed: R43.2, VT8.3 (B)
unnamed: R60.2, VT10.3 (B)
unnamed: R62.1, R80.2, VT9.3 (B)
unnamed: R80.1, VT8.2 (C)
unnamed: R82.1, VT9.2 (C)
unnamed: R86.2, VD8.2 (A)
P0: DD34.14 (Qb), DD43.14 (I0c)
P1: DD34.12 (Qd), DD43.5 (I0b)
P2: DD34.13 (Qc), DD43.2 (I0a)
Q1: DD54.3 (D0), DD59.14 (IO6)
Q2: DD54.4 (D1), DD59.13 (IO7)
Q3: DD54.6 (D2), DD59.12 (IO8)
Q4: DD54.11 (D3), DD59.15 (IO5)
R: DD43.7 (Zb), R16.2
RAMM1: DD10.13, DD50.3 (C), DD50.11 (C)
RAS: DD11.11, DD15.1 (S), DD16.1 (S), DD17.1 (S), DD18.1 (S), DD45.2 (A1), XP4.b8, XP5.b8, XP7.b8
RB: DD67.5, R63.2, XP4.a4, XP5.a4, XP7.a4
RDMEM: DD10.10, DD12.2, DD69.4
RDT: DD63.9, DD63.10, R89.1, XP2.30, XP11.30
RD_FFFD: DD48.5, DD52.7 (O7)
RO: R4.1, XP1.b29, XP3.4, XP6.b29
ROM: C16.2, DD12.1, DD49.11, DD67.6, DD67.9, DD68.11
ROM1: DD46.10 (Q3), DD49.5, DD51.9 (IOA5), DD66.5
RTH: R68.1, R71.2, R72.1, XP1.a26, XP6.a26
RWD: DD54.12 (Q4), DD54.14 (D5), DD59.5 (I5), DD60.27 (RWD)
S: DD56.2 (D), DD56.6 (~Q), DD60.26 (S)
SC18: DD48.3, DD51.18 (BDIR)
SC20: DD48.6, DD51.20 (BC1)
SCR: DD17.3 (I1a), DD46.15 (Q5), DD51.11 (IOA3)
SID: DD41_1.10, XP2.32, XP11.32
STB: DD61.2, R42.1, XP1.a16, XP6.a16
STP: DD55.4 (~S), DD61.12, XP2.20, XP11.20
SYNC: R20.1, VT2.2 (C), XP1.a28, XP3.8, XP6.a28
TIN: DD37.14 (I0c), DD70.8, DD70.10
TM9: DD57.9 (Cp), DD65.12 (O3)
TR0: DD60.34 (~TR0), R78.1, XP2.26, XP11.26
TRB: DD9.8 (~Q), DD9.12 (D), DD30.8 (IN)
TX: DD47.15 (Q5), R43.1
TXD: R79.2, R82.2, XP1.b28, XP6.b28
T_IN: C13.2, XP1.a25, XP6.a25
T_OUT: C11.1, XP1.b25, XP6.b25
V0: DD5.3 (QA), DD19.2 (I0a)
V1: DD5.2 (QB), DD19.5 (I0b)
V2: DD5.6 (QC), DD13.9
V3: DD5.7 (QD), DD17.5 (I0b)
V4: DD6.3 (QA), DD17.14 (I0c), DD31.9
V5: DD6.2 (QB), DD17.2 (I0a), DD31.10
V6: DD6.6 (QC), DD12.10, DD13.1, DD19.3 (I1a), DD19.14 (I0d)
V7: DD6.7 (QD), DD12.9, DD19.6 (I1b), DD19.11 (I0c)
VCC: C4.2, C5.2, C6.2, C7.2, C8.2, C10.1, C14.2, C15.2, C20.2, C22.2, C23.2, C24.2, C25.2, C26.2, C27.2, C28.2, C29.2, C30.2, C31.2, C32.2, C33.2, C34.2, C35.2, C36.2, C37.2, C38.2, C39.2, C40.2, C41.2, C42.2, C43.2, C44.2, C45.2, C46.2, DD1.14 (VCC), DD2.1 (~R), DD2.4 (~S), DD2.13 (~R), DD2.14 (VCC), DD3.1 (B), DD3.4 (DOWN), DD3.9 (D), DD3.10 (C), DD3.11 (~LOAD), DD3.15 (A), DD3.16 (VCC), DD4.1 (B), DD4.4 (DOWN), DD4.15 (A), DD4.16 (VCC), DD5.4 (DOWN), DD5.16 (VCC), DD6.4 (DOWN), DD6.16 (VCC), DD7.16 (VDD), DD8.1 (~R), DD8.4 (~S), DD8.10 (~S), DD8.13 (~R), DD8.14 (VCC), DD9.1 (~R), DD9.14 (VCC), DD10.14 (VCC), DD11.10, DD11.13, DD11.14 (VCC), DD12.14 (VCC), DD13.14 (VCC), DD14.14 (VCC), DD15.16 (VCC), DD16.16 (VCC), DD17.10 (I1d), DD17.13 (I1c), DD17.16 (VCC), DD18.16 (VCC), DD19.10 (I1c), DD19.13 (I1d), DD19.16 (VCC), DD20.11 (VCC), DD21.8 (VCC), DD22.8 (VCC), DD23.8 (VCC), DD24.8 (VCC), DD25.8 (VCC), DD26.8 (VCC), DD27.8 (VCC), DD28.8 (VCC), DD29.1 (VPP), DD29.31 (~PGM), DD29.32 (VCC), DD30.22 (I/O), DD30.24 (VCC), DD31.14 (VCC), DD32.16 (VCC), DD33.16 (VCC), DD34.16 (VCC), DD35.1 (~Mr), DD35.16 (VCC), DD36.16 (VCC), DD37.16 (VCC), DD38.20 (VCC), DD39.9 (Clr), DD39.16 (VCC), DD40.8 (OE), DD40.14 (VCC), DD41.24 (VCC), DD41_1.14 (VCC), DD41_2.14 (VCC), DD42.2 (D), DD42.10 (~S), DD42.14 (VCC), DD43.16 (VCC), DD44.16 (VCC), DD45.16 (VCC), DD46.16 (VCC), DD47.16 (VCC), DD48.14 (VCC), DD49.14 (VCC), DD50.13 (~R), DD50.14 (VCC), DD51.3 (VCC), DD51.17 (A8), DD52.6 (E3), DD52.16 (VCC), DD53.20 (VCC), DD54.1 (~Mr), DD54.16 (VCC), DD55.10 (~S), DD55.13 (~R), DD55.14 (VCC), DD56.1 (~R), DD56.4 (~S), DD56.10 (~S), DD56.12 (D), DD56.14 (VCC), DD57.16 (VCC), DD58.20 (VCC), DD59.20 (VCC), DD60.21 (VCC), DD60.22 (~TST), DD61.14 (VCC), DD62.8 (OE), DD62.14 (VCC), DD63.14 (VCC), DD64.1 (~MR), DD64.7 (CEP), DD64.9 (~PE), DD64.10 (CET), DD64.16 (VCC), DD65.16 (VCC), DD66.14 (VCC), DD67.14 (VCC), DD68.14 (VCC), DD69.14 (VCC), DD70.14 (VDD), L1.2, NR1.1 (common), R10.1, R20.2, R22.2, R23.2, R24.2, R25.2, R27.1, R33.2, R36.2, R42.2, R49.1, R50.1, R51.1, R52.1, R53.1, R54.2, R59.1, R61.2, R62.2, R65.1, R67.1, R74.2, R75.2, R77.2, R78.2, R83.2, R84.2, R87.2, R88.1, R89.2, R90.2, VD1.1 (K), VD7.1 (K), VD15.2 (A), VT3.2 (C), VT4.2 (C), VT5.2 (C), VT6.2 (C), VT9.1 (E), XP1.a21, XP1.a22, XP1.b21, XP1.b22, XP3.1, XP4.b3, XP5.b3, XP6.a21, XP6.a22, XP6.b21, XP6.b22, XP7.b3, XP9.1
VF: DD55.1 (~R), DD60.33 (~VFOE), R88.2
VIDEO: R8.1, XP1.a30, XP3.10, XP6.a30
WPG: DD61.8, XP2.24, XP11.24
WRFE: DD10.1, DD35.9 (Cp)
WRP: DD60.36 (~WRPT), R90.1, VD17.1 (K), XP2.28, XP11.28
WR_1FFD: DD47.9 (Cp), DD52.15 (O0)
WR_7FFD: DD45.15 (OEb), DD52.13 (O2)
WR_BFFD: DD48.1, DD52.11 (O4)
WR_EN: DD30.5 (IN), DD67.8
WR_FFFD: DD48.2, DD48.4, DD52.9 (O6)
Y: DD43.9 (Zd), R17.2, R18.2, R19.2, XP3.7
~BAK: DD20.23 (~BUSACK), XP4.b26, XP5.b26, XP7.b26
~BC: C1.1, DD5.5 (UP), DD8.5 (Q), DD13.4
~BK: DD5.10 (C), DD6.10 (C), DD8.9 (Q), DD13.5
~BRD: DD13.6, DD30.9 (IN), DD33.10 (S), DD34.10 (S), DD69.9
~BRQ: DD20.25 (~BUSRQ), R24.1, XP4.b19, XP5.b19, XP7.b19
~CAS: DD11.8, DD21.15 (~CAS), DD22.15 (~CAS), DD23.15 (~CAS), DD24.15 (~CAS), DD25.15 (~CAS), DD26.15 (~CAS), DD27.15 (~CAS), DD28.15 (~CAS)
~CC: DD31.6, DD42.13 (~R), XP1.a24, XP3.3, XP6.a24
~CLK: DD2.2 (D), DD2.6 (~Q), DD3.5 (UP), DD39.7 (Clk)
~CSKB: DD36.15 (OE), DD37.15 (OE), DD66.3
~CSR: DD12.3, R58.2, XP4.b25, XP5.b25, XP7.b25
~DOS: DD50.6 (~Q), DD65.5 (E2), DD69.12, XP4.b4, XP5.b4, XP7.b4
~H1M: DD1.2, DD17.15 (OE), DD18.15 (OE)
~H2: DD1.8, DD13.10, DD31.13, DD53.11 (Cp)
~H6: DD1.10, DD2.10 (~S), DD31.5
~HALT: DD20.18 (~HALT), XP4.a15, XP5.a15, XP7.a15
~INT: DD20.16 (~INT), R81.2, XP4.a13, XP5.a13, XP7.a13
~IORQGE: DD32.5 (E2), DD65.4 (E1), R57.2, XP4.b13, XP5.b13, XP7.b13
~IORQ: DD20.20 (~IORQ), DD30.4 (IN/PD), R57.1, XP4.a17, XP5.a17, XP7.a17
~KC: DD2.11 (C), DD7.2 (Enable), DD31.8, DD42.4 (~S), DD42.12 (D), DD55.11 (C), XP1.a23, XP3.2, XP6.a23
~M1: DD10.12, DD13.13, DD20.27 (~M1), DD30.10 (IN), DD32.6 (E3), DD67.2, XP4.a24, XP5.a24, XP7.a24
~MREQ: DD10.9, DD20.19 (~MREQ), DD67.10, DD67.13, XP4.a16, XP5.a16, XP7.a16
~NMI: DD20.17 (~NMI), R56.1, XP4.a14, XP5.a14, XP7.a14
~RAM: DD10.11, DD30.6 (IN), DD38.1 (OE), DD69.6
~RAS: DD11.12, DD21.4 (~RAS), DD22.4 (~RAS), DD23.4 (~RAS), DD24.4 (~RAS), DD25.4 (~RAS), DD26.4 (~RAS), DD27.4 (~RAS), DD28.4 (~RAS), DD30.17 (I/O)
~RDR: DD29.22 (~CE), DD41.1 (CLK/IN), DD50.10 (~S), R58.1, XP4.b15, XP5.b15, XP7.b15
~RD: DD10.8, DD12.12, DD14.2, DD14.12, DD20.21 (~RD), DD60.4 (~RD), XP4.a18, XP5.a18, XP7.a18
~RES: C9.1, DD20.26 (~RESET), DD46.1 (~Mr), DD47.1 (~Mr), DD50.1 (~R), DD51.16 (~RESET), DD57.1 (~Mr), R22.1, VD1.2 (A), XP1.b23, XP4.b20, XP5.b20, XP6.b23, XP7.b20
~RFSH: DD12.13, DD20.28 (~RFSH), XP4.a25, XP5.a25, XP7.a25
~WAIT: DD20.24 (~WAIT), R23.1, VD2.2 (A), XP4.a21, XP5.a21, XP7.a21
~WE: DD21.3 (~WE), DD22.3 (~WE), DD23.3 (~WE), DD24.3 (~WE), DD25.3 (~WE), DD26.3 (~WE), DD27.3 (~WE), DD28.3 (~WE), DD30.19 (I/O), R36.1
~WRBFR: DD30.16 (I/O), DD38.11 (LE)
~WRPRT: DD14.8, DD58.11 (Cp)
~WR: DD10.3, DD14.9, DD20.22 (~WR), DD52.1 (A0), DD60.2 (~WR), DD65.3 (A2), XP4.a19, XP5.a19, XP7.a19

Notes on the sheet:
Краевой разъем шины
Триггер выбора 1-DOS 0-SOS
Переключение ПЗУ 48/128
Переключение CPU/TV
Turbo/Normal
Блок записи в 7FFD
Разделительный резистор для системной шины
Триггер отслеживающий нажатие magic
Дешифратор AY
Переключение экранов
Системный краевой разъем
Необязательный резистор, требуется только для доработки выбора порта #7FFD по команде по команде "OUT(#FD),A", где необходимо впаять резистор в разрез между A14 и второй ножки DD52. Чтобы упростить задачу добавлен резистор типоразмера 0805, при необходимости можно перерезать дорожку между контактам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
7FFD
Мультиплексор старшего разряда адреса ОЗУ
Системный разъем DIP
1FFD
~{KC} - Кадровые синхроимпульсы ~{CC} - Строчные синхроимпульсы ~{BC} - Бордюр BRD[2:0] - BORDER P[2:0] - PAPER I[2:0] - INK Атрибуты: D[2:0] - INK D[5:3] - PAPER D6 - BRIGHT D7 - FLASH Адресация VRAM: H3 - MA0 - A0 H4 - MA1 - A1 H5 - MA2 - A2 H6 - MA3 - A3 H7 - MA4 - A4 -------------- V3 - MA5 - A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
ProfROM
FF (Аттрибуты экрана)
Свободная линия D5. Можно перерезать перемычку JP5 и использовать для доработок, к примеру для подключения кнопки джойстика FIRE2.
Разъем шины DIP 3 ряда ножек
Селектор окна C000-FFFF
Выбор между классическим подключением ZS Scorpion микросхемы AY-3-8912 BAC и более распространенном ABC. Для выбора ABC необходимо разрезать перемычки JP1, JP4 и запаять перемычки JP2,JP3
Блокировка ПЗУ 0-3FFF
Дешифратор портов оканчивающихся на FD
Разъем шины DIP 2 ряда ножек
Комутатор страниц ОЗУ
Селектор окна 3D00 в ПЗУ
